Bui-Diep/FPGA_TOPIC/Hardware/Circuit design on Altium/DataSheet/logic/CMOS Logic.png

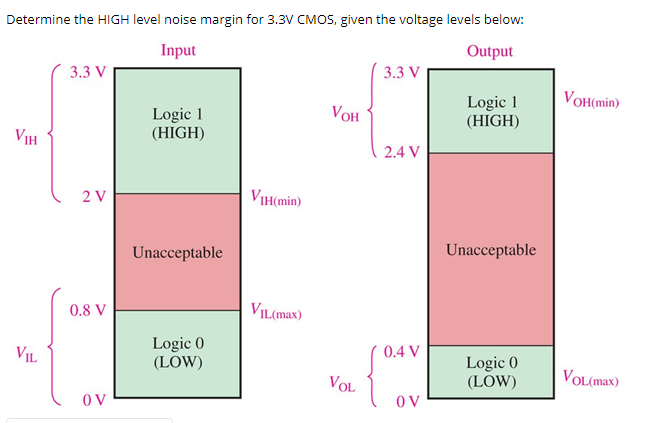
Hardware/Circuit design on Altium/DataSheet/logic/CMOS Logic.png
