Bui-Diep/FPGA_TOPIC/Hardware/Circuit design on Altium/DataSheet/logic/IC Logic.jpg

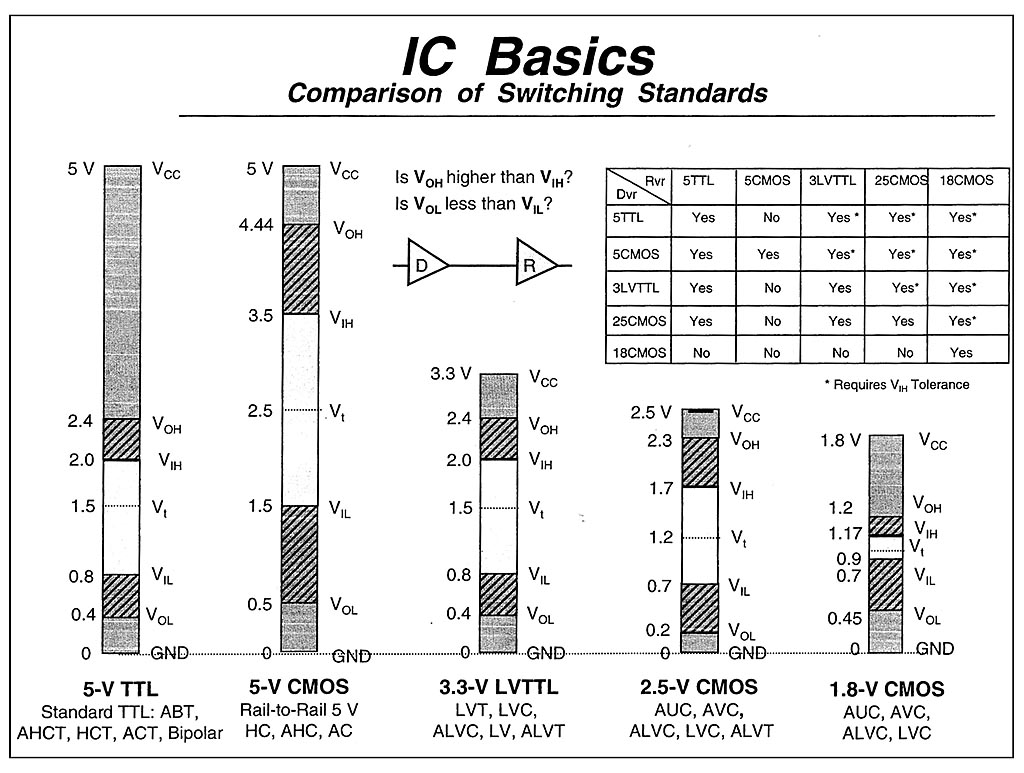
Hardware/Circuit design on Altium/DataSheet/logic/IC Logic.jpg
