Bui-Diep/FPGA_TOPIC/Hardware/FPGA programming/UART-communication/uart_controller_rx.vhd

library ieee;
  use IEEE.std_logic_1164.all;
  use IEEE.std_logic_arith.all;
  use IEEE.std_logic_unsigned.all;

entity uart_controller_rx is
  generic (
    d_bit : integer := 8;
    sb_tick : integer := 16
  );
  port (
		ckht : in std_logic;
		rst : in std_logic;
		rx : in std_logic;
		s_tick : in std_logic;

		rx_done_tick : out std_logic;
		rx_data : out std_logic_vector(7 downto 0)
  );
end uart_controller_rx;

architecture rtl of uart_controller_rx is
type state_type is (idle, start, data, stop); -- khai bao mang (bao gom 4 trang thai)
signal state_r : state_type;  -- khai bao tin hieu hien tai
signal state_n : state_type;  -- khai bao tin hieu trang thai can chuyen toi

signal s_r, s_n : unsigned (3 downto 0);  -- thanh ghi s dem so tick lay mau 
signal n_r, n_n : unsigned (2 downto 0);  -- thanh ghi n dem so bit data da nhan duoc
signal b_r, b_n : std_logic_vector (7 downto 0);  -- thanh ghi b luu gia tri data
begin
process (ckht, rst)
begin
    if rst = '0' then -- khi co tin hieu reset he thong tro ve trang thai cho
		state_r <= idle;
		s_r <= (others => '0');
		n_r <= (others => '0');
		b_r <= (others => '0');
    elsif falling_edge (ckht) then  --khi khong co reset va khi co suon duoi cua ckht thi 
		state_r <= state_n;           --trang thai la trang thai moI
		s_r <= s_n;     				-- trang thai r <= n mỗi khi có xung ckht
		n_r <= n_n;
		b_r <= b_n;
    end if;
    end process;
process(state_r, s_r, n_r, b_r, s_tick, rx)
begin
	state_n <= state_r;
	b_n <= b_r;
	s_n <= s_r;
	n_n <= n_r;
  rx_done_tick <= '0';
case state_r is
	when idle =>
		if (rx = '0') then
			state_n <= start;
			s_n <= (others => '0');
		end if;
	when start =>
		if (s_tick = '1') then  -- tich chi bang 1 trong 1 chu ky cua xung (ckht)
			if (s_r = 7) then
				state_n <= data;
				s_n <= (others => '0');
				n_n <= (others => '0');
			else s_n <= s_r + 1;	-- trong mot chu ky cua (ckht) thi moi cong mot lan
			end if;
		end if;
	when data =>
		if (s_tick = '1') then 	-- kiem tra xem có xung tick khong
			if (s_r = 15) then -- moi lan co xung tick thi s_r se tang len 1
				s_n <= (others => '0');	-- reset lai bo dem xung tick
				b_n <= rx & b_r(7 downto 1);
				if (n_r = d_bit - 1) then
					state_n <= stop;
				else n_n <= n_r + 1;
				end if;
			else s_n <= s_r + 1;
			end if;
		end if;
	when stop =>
		if (s_tick = '1') then
			if (s_r = sb_tick - 1) then
				state_n <= idle;
				rx_done_tick <= '1';
			else s_n <= s_r + 1;
			end if;
		end if;
end case;
end process ;
rx_data <= b_r;
end architecture;
