Bui-Diep/FPGA_TOPIC/Hardware/FPGA programming/Cache-modul-FIFO-LIFO/lifo_cache.vhd

-- LIFO cache with 8-bit data and 8 entries
library ieee;
use ieee.std_logic_1164.all;

entity lifo_cache is
    port (
        clk : in std_logic;
        reset : in std_logic;
        push : in std_logic;
        pop : in std_logic;
        data_in : in std_logic_vector(7 downto 0);
        data_out : out std_logic_vector(7 downto 0)
    );
end lifo_cache;

architecture lifo_cache_arch of lifo_cache is
    type cache_array is array (0 to 7) of std_logic_vector(7 downto 0);
    signal cache : cache_array;
    signal top_of_stack : integer range 0 to 7;
begin
    -- push data onto the cache
    process (clk, reset, push)
    begin
        if (reset = '1') then
            top_of_stack <= 0;
        elsif (rising_edge(clk)) then
            if (push = '1') then
                if (top_of_stack < 7) then
                    top_of_stack <= top_of_stack + 1;
                end if;
                cache(top_of_stack) <= data_in;
            end if;
        end if;
    end process;

    -- pop data from the cache
    process (clk, reset, pop)
    begin
        if (reset = '1') then
            data_out <= (others => '0');
        elsif (rising_edge(clk)) then
            if (pop = '1') then
                if (top_of_stack > 0) then
                    top_of_stack <= top_of_stack - 1;
                end if;
                data_out <= cache(top_of_stack);
            end if;
        end if;
    end process;
end lifo_cache_arch;

/* This program defines an entity called lifo_cache with input ports clk, reset, push, pop, data_in, and output port data_out. It has an internal type called cache_array that is an array of 8 8-bit std_logic_vectors. It also has an internal signal called cache that is of type cache_array, and an internal signal called top_of_stack that is an integer ranging from 0 to 7.

    The program has two processes: one for pushing data onto the cache, and one for popping data from the cache. The push process checks for a rising edge on the clock and pushes the data_in onto the top of the stack if the push input is high. The pop process works similarly, but pops the data from the top of the stack if the pop input is high.*/  
